ysoldak/projects/FL Fw190 Dora 850mm/img/Cockpit_side.jpg

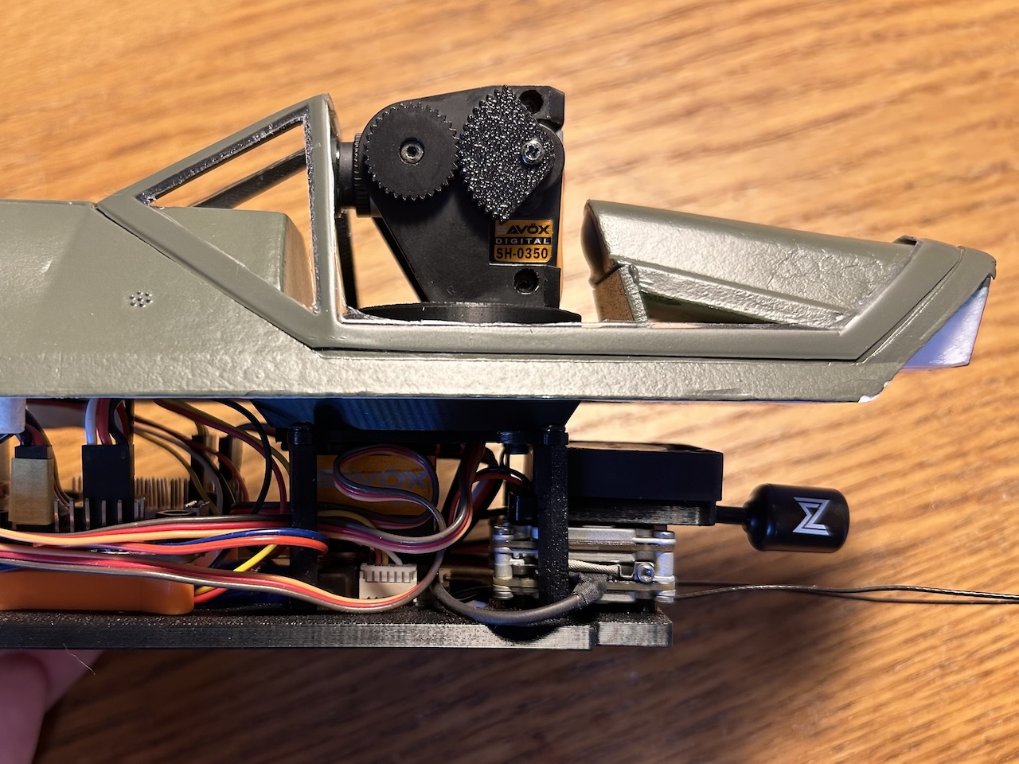
FL Fw190 Dora 850mm/img/Cockpit_side.jpg
