ysoldak/projects/FL P-51D Mustang 850mm/img/Vista_fan.JPG

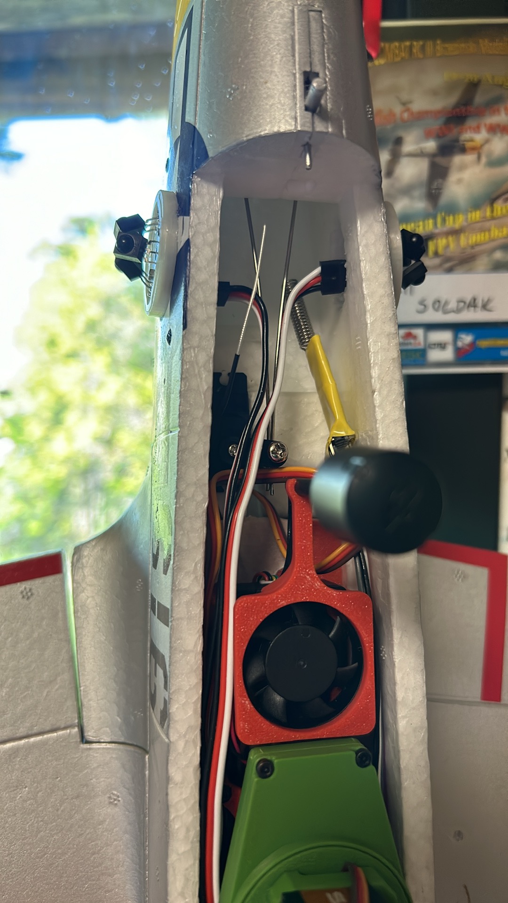
FL P-51D Mustang 850mm/img/Vista_fan.JPG
