ysoldak/projects/FL P-51D Mustang 850mm/stl/FL P-51D Mustang 850mm Base.stl

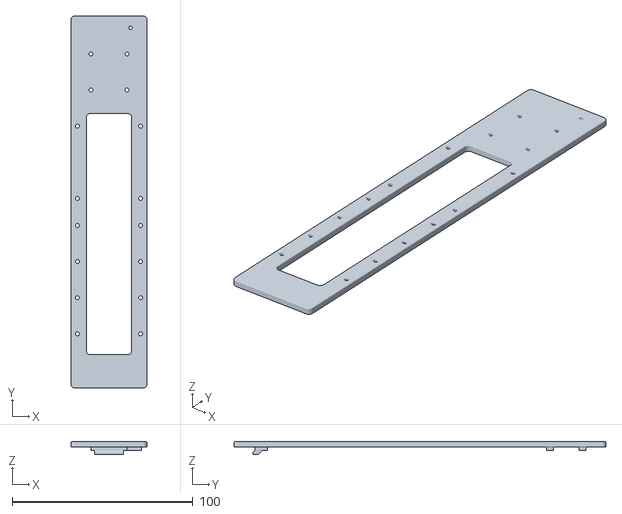
[picture p42: CAD file, 2024-08-29]
FL P-51D Mustang 850mm/stl/FL P-51D Mustang 850mm Base.stl
42.0 x 206.0 x 7.00
