ysoldak/projects/FL Fw190 Dora 850mm/stl/FL Fw190 Dora 850mm Base.stl

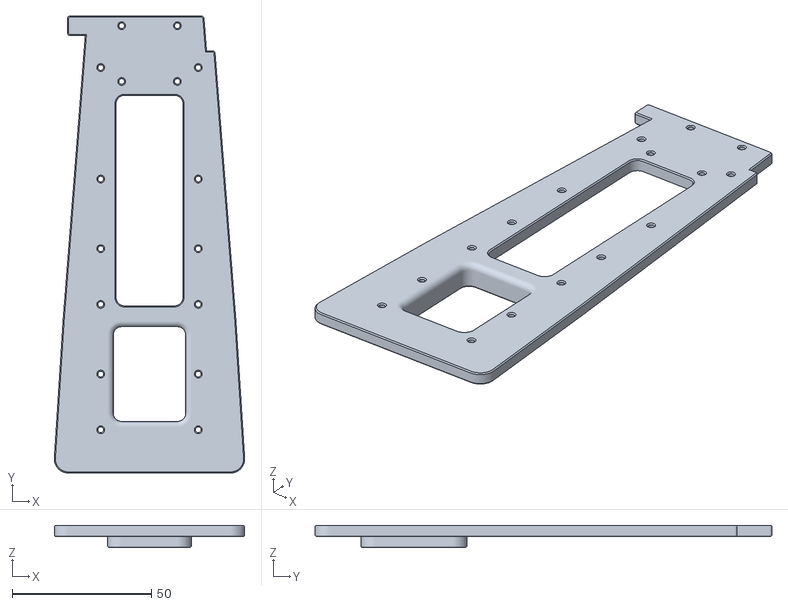
[picture p43: CAD file, 2024-08-22]
FL Fw190 Dora 850mm/stl/FL Fw190 Dora 850mm Base.stl
68.3 x 164.0 x 8.00
