ysoldak/projects/FL P-51D Mustang 850mm/stl/FL P-51D Mustang 850mm Standoff 8mm.stl

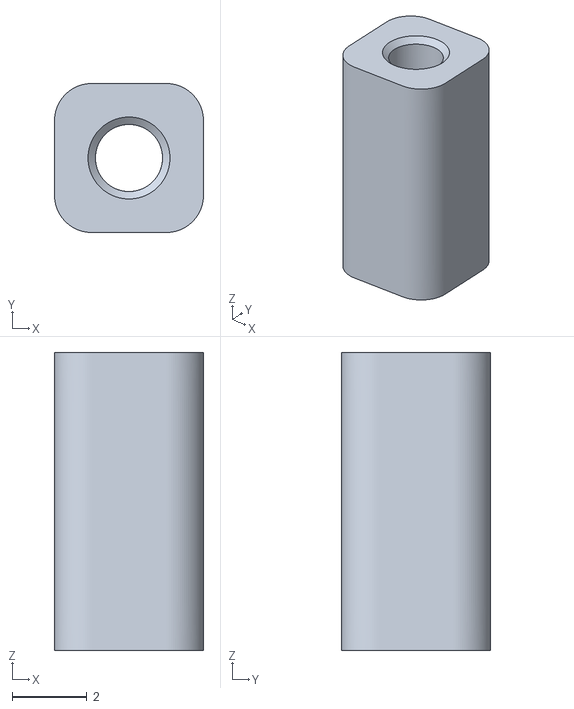
[picture p44: CAD file, 2024-08-29]
FL P-51D Mustang 850mm/stl/FL P-51D Mustang 850mm Standoff 8mm.stl
4.00 x 4.00 x 8.00
