ysoldak/projects/FL Fw190 Dora 850mm/stl/FL Fw190 Dora 850mm Cockpit Frame.stl

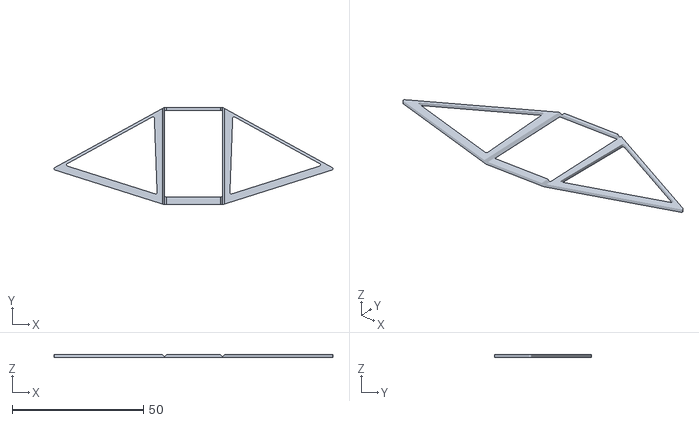
[picture p45: CAD file, 2024-08-22]
FL Fw190 Dora 850mm/stl/FL Fw190 Dora 850mm Cockpit Frame.stl
106.3 x 37.1 x 1.00
