ysoldak/projects/FL Fw190 Dora 850mm/stl/FL Fw190 Dora 850mm Standoff 27mm.stl

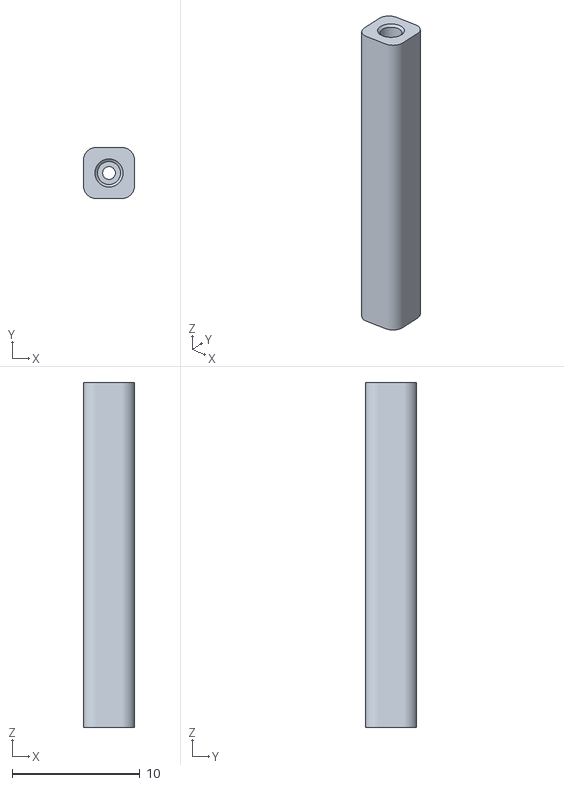
[picture p46: CAD file, 2024-08-22]
FL Fw190 Dora 850mm/stl/FL Fw190 Dora 850mm Standoff 27mm.stl
4.00 x 4.00 x 27.0
